romychs/Scorpion256TPlus/KiCAD/Scorpion-256-Turbo.kicad_sch

## KiCad design KiCAD/Scorpion-256-Turbo.kicad_sch (2025-11-04)

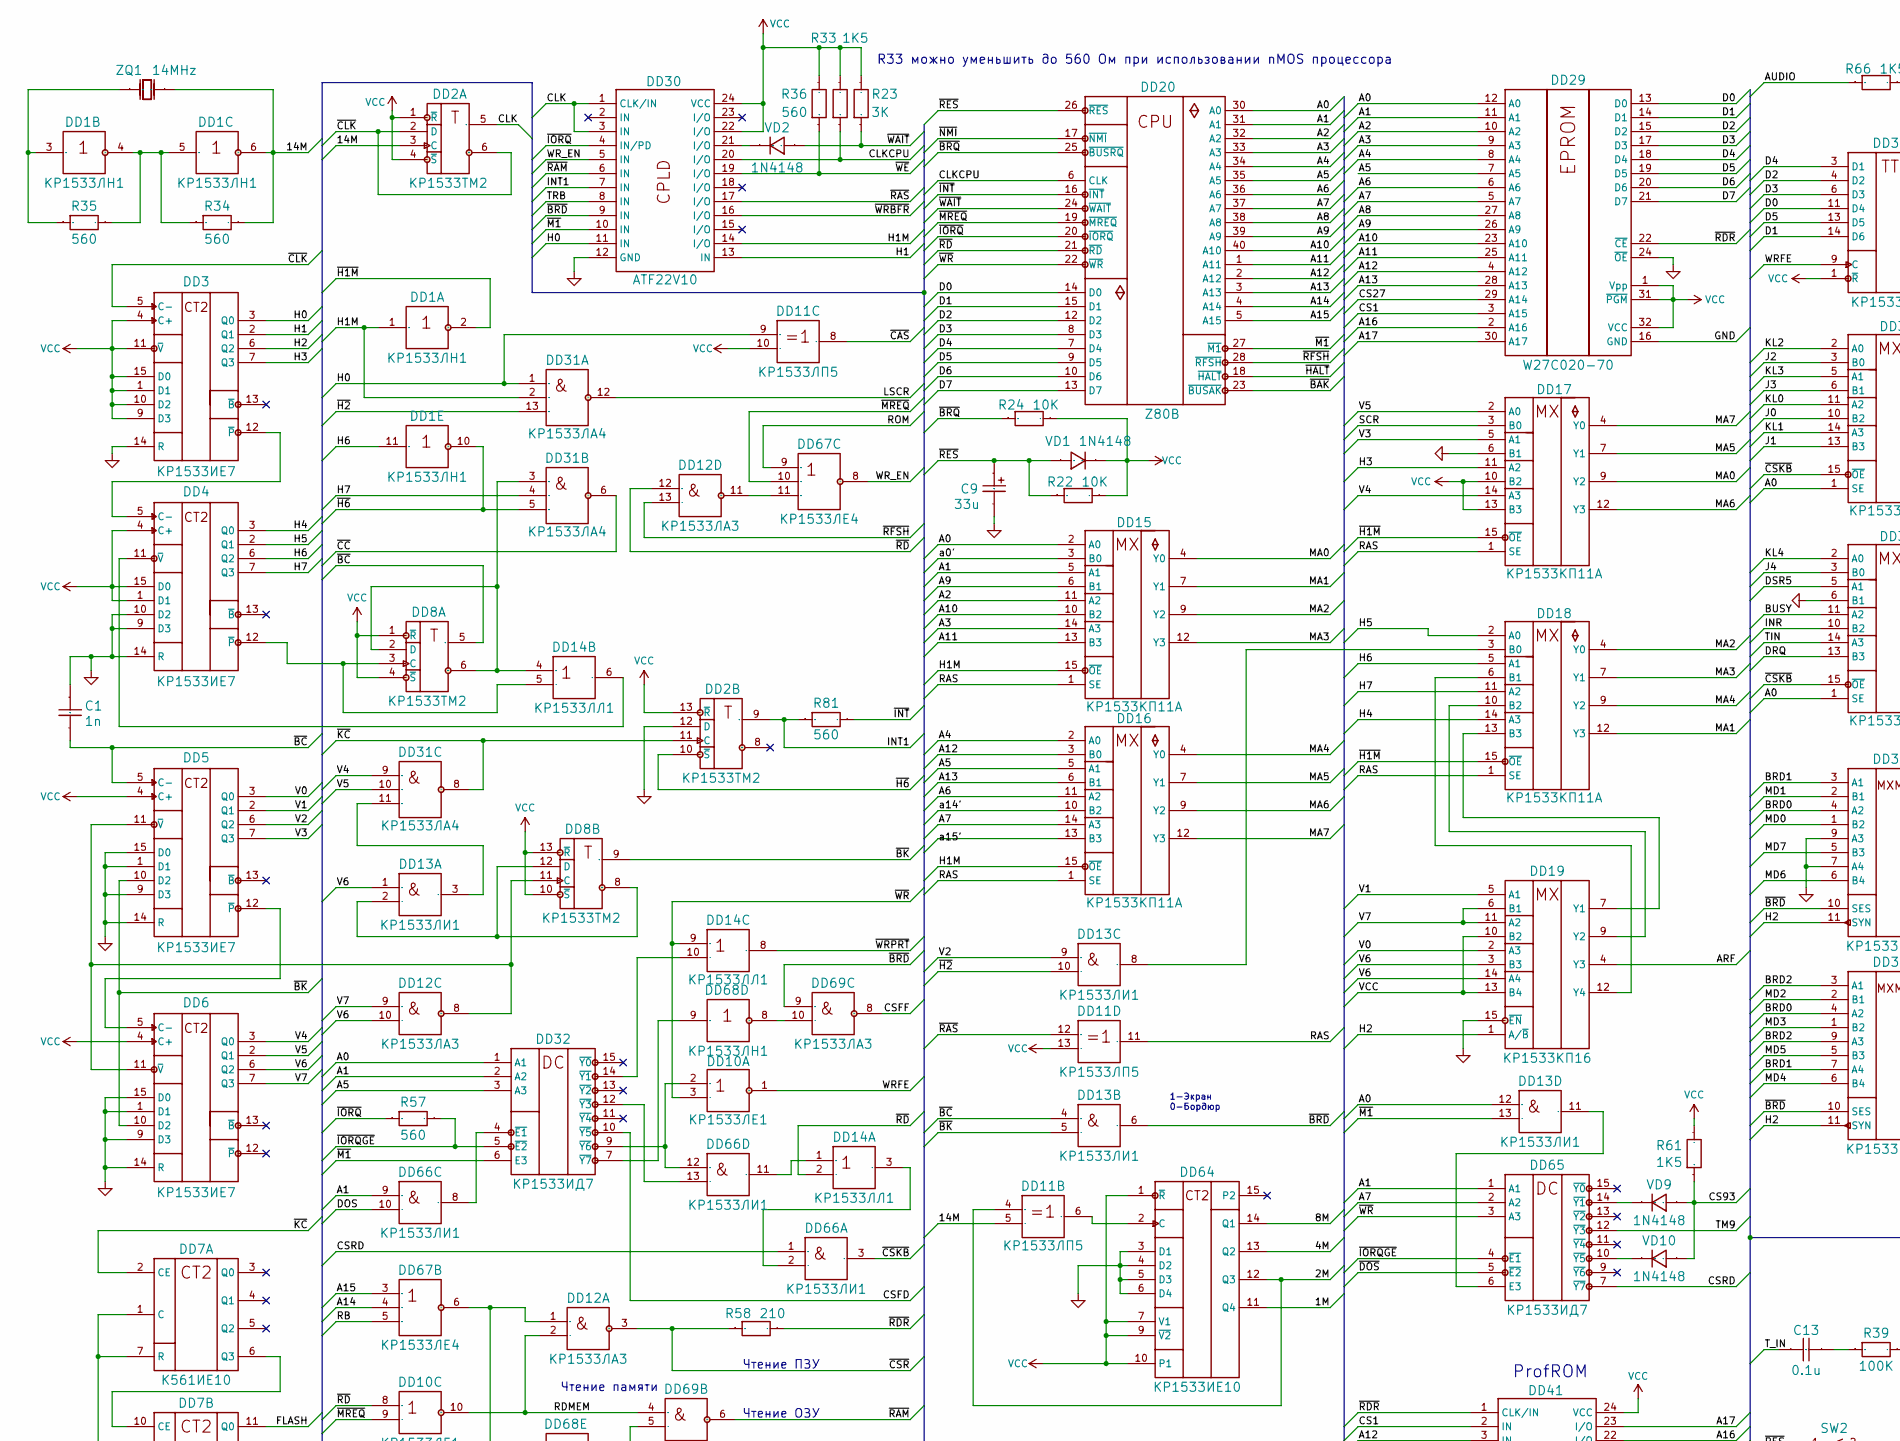
[picture p6: schematic Scorpion-256-Turbo.kicad_sch, part in row 1, column 1]

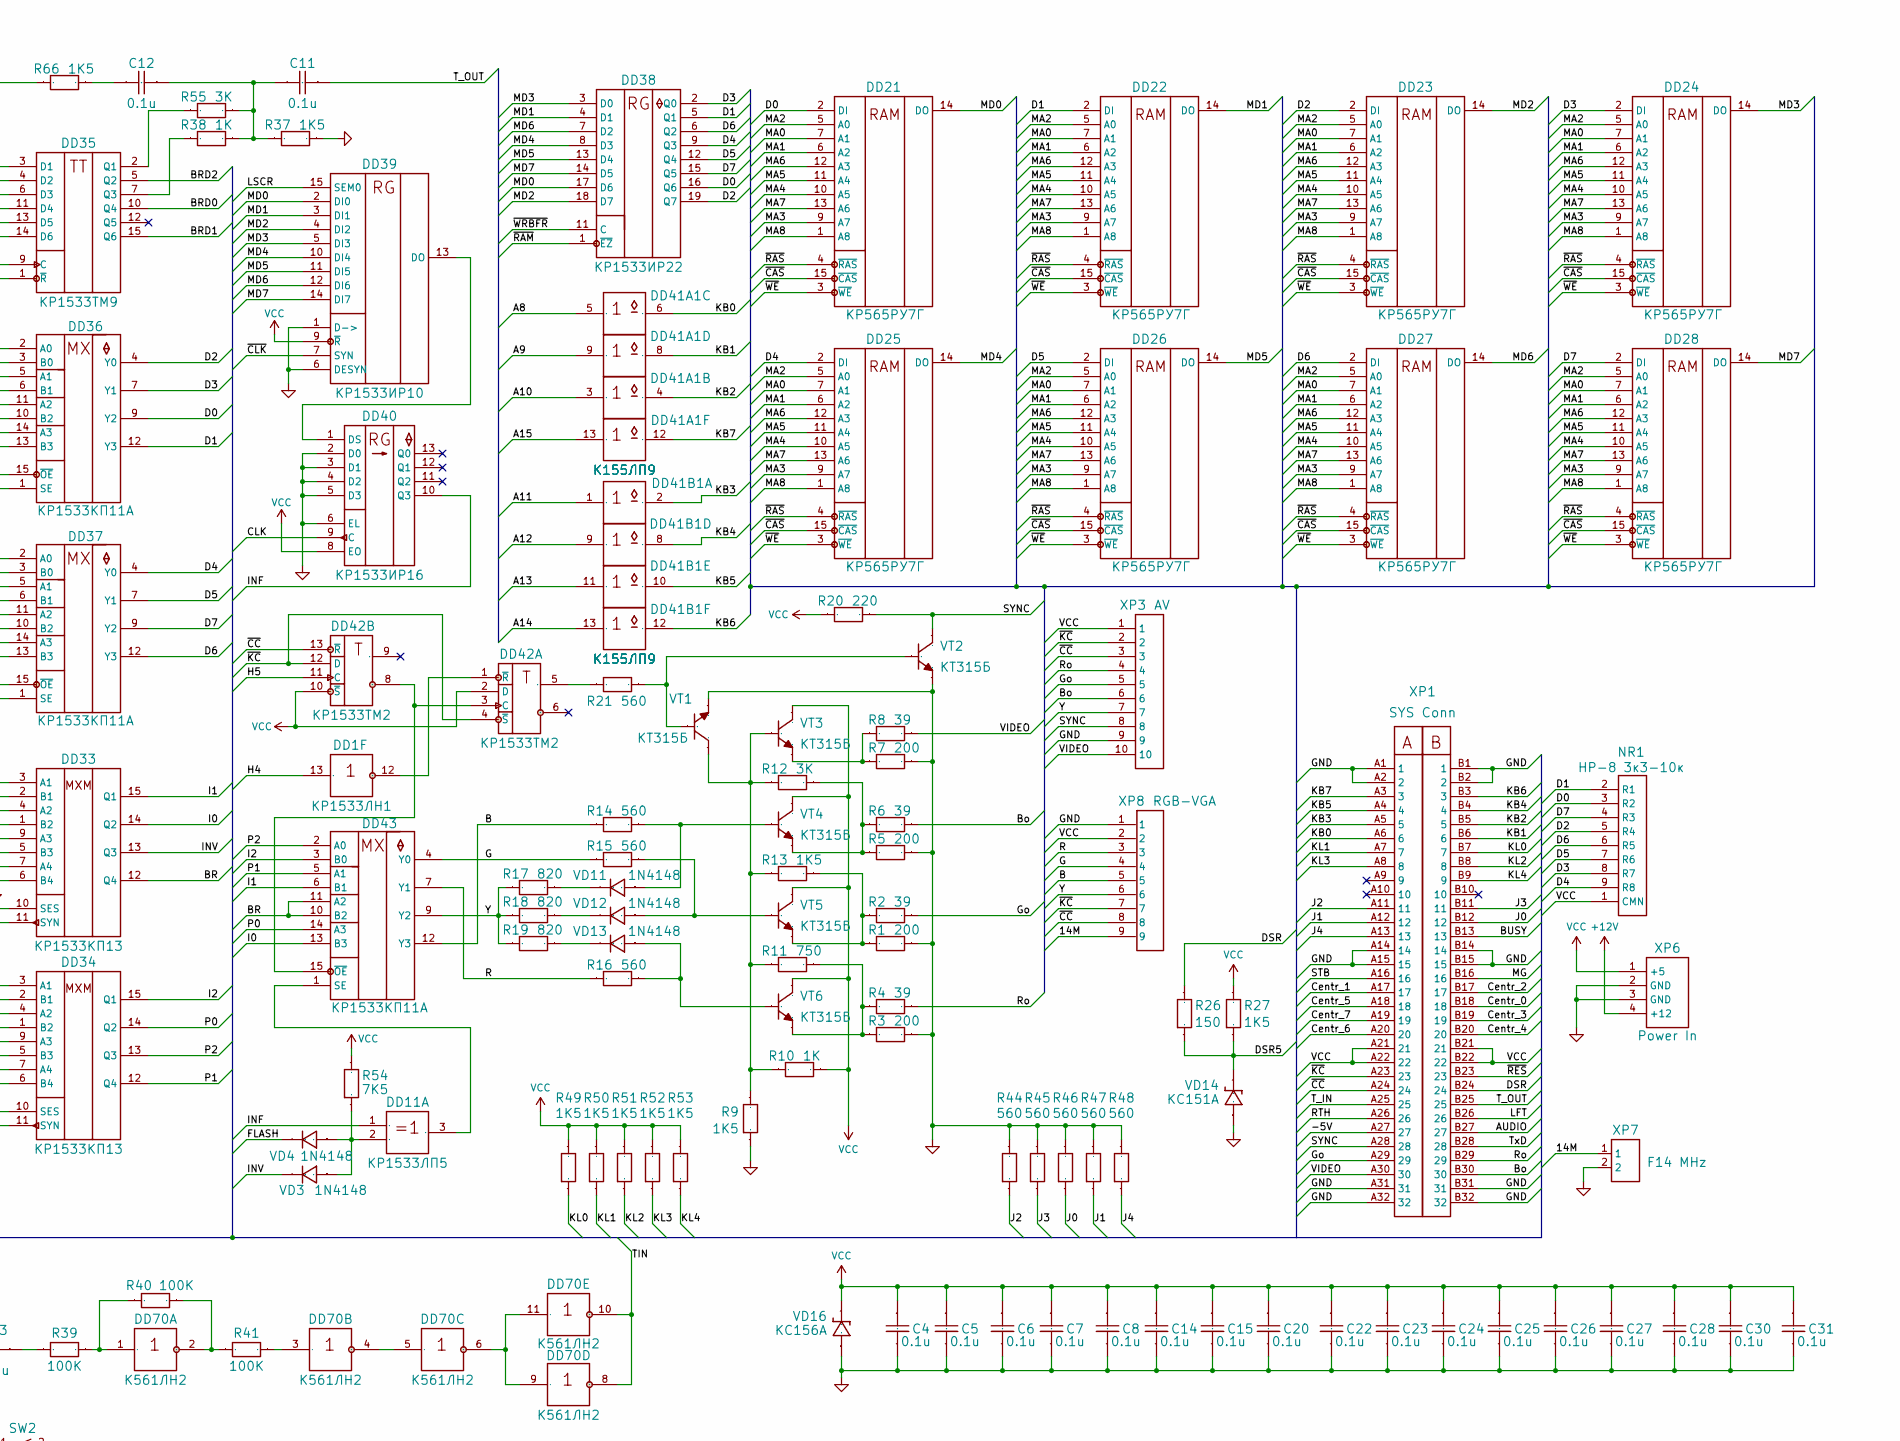
[picture p7: schematic Scorpion-256-Turbo.kicad_sch, part in row 1, column 2]

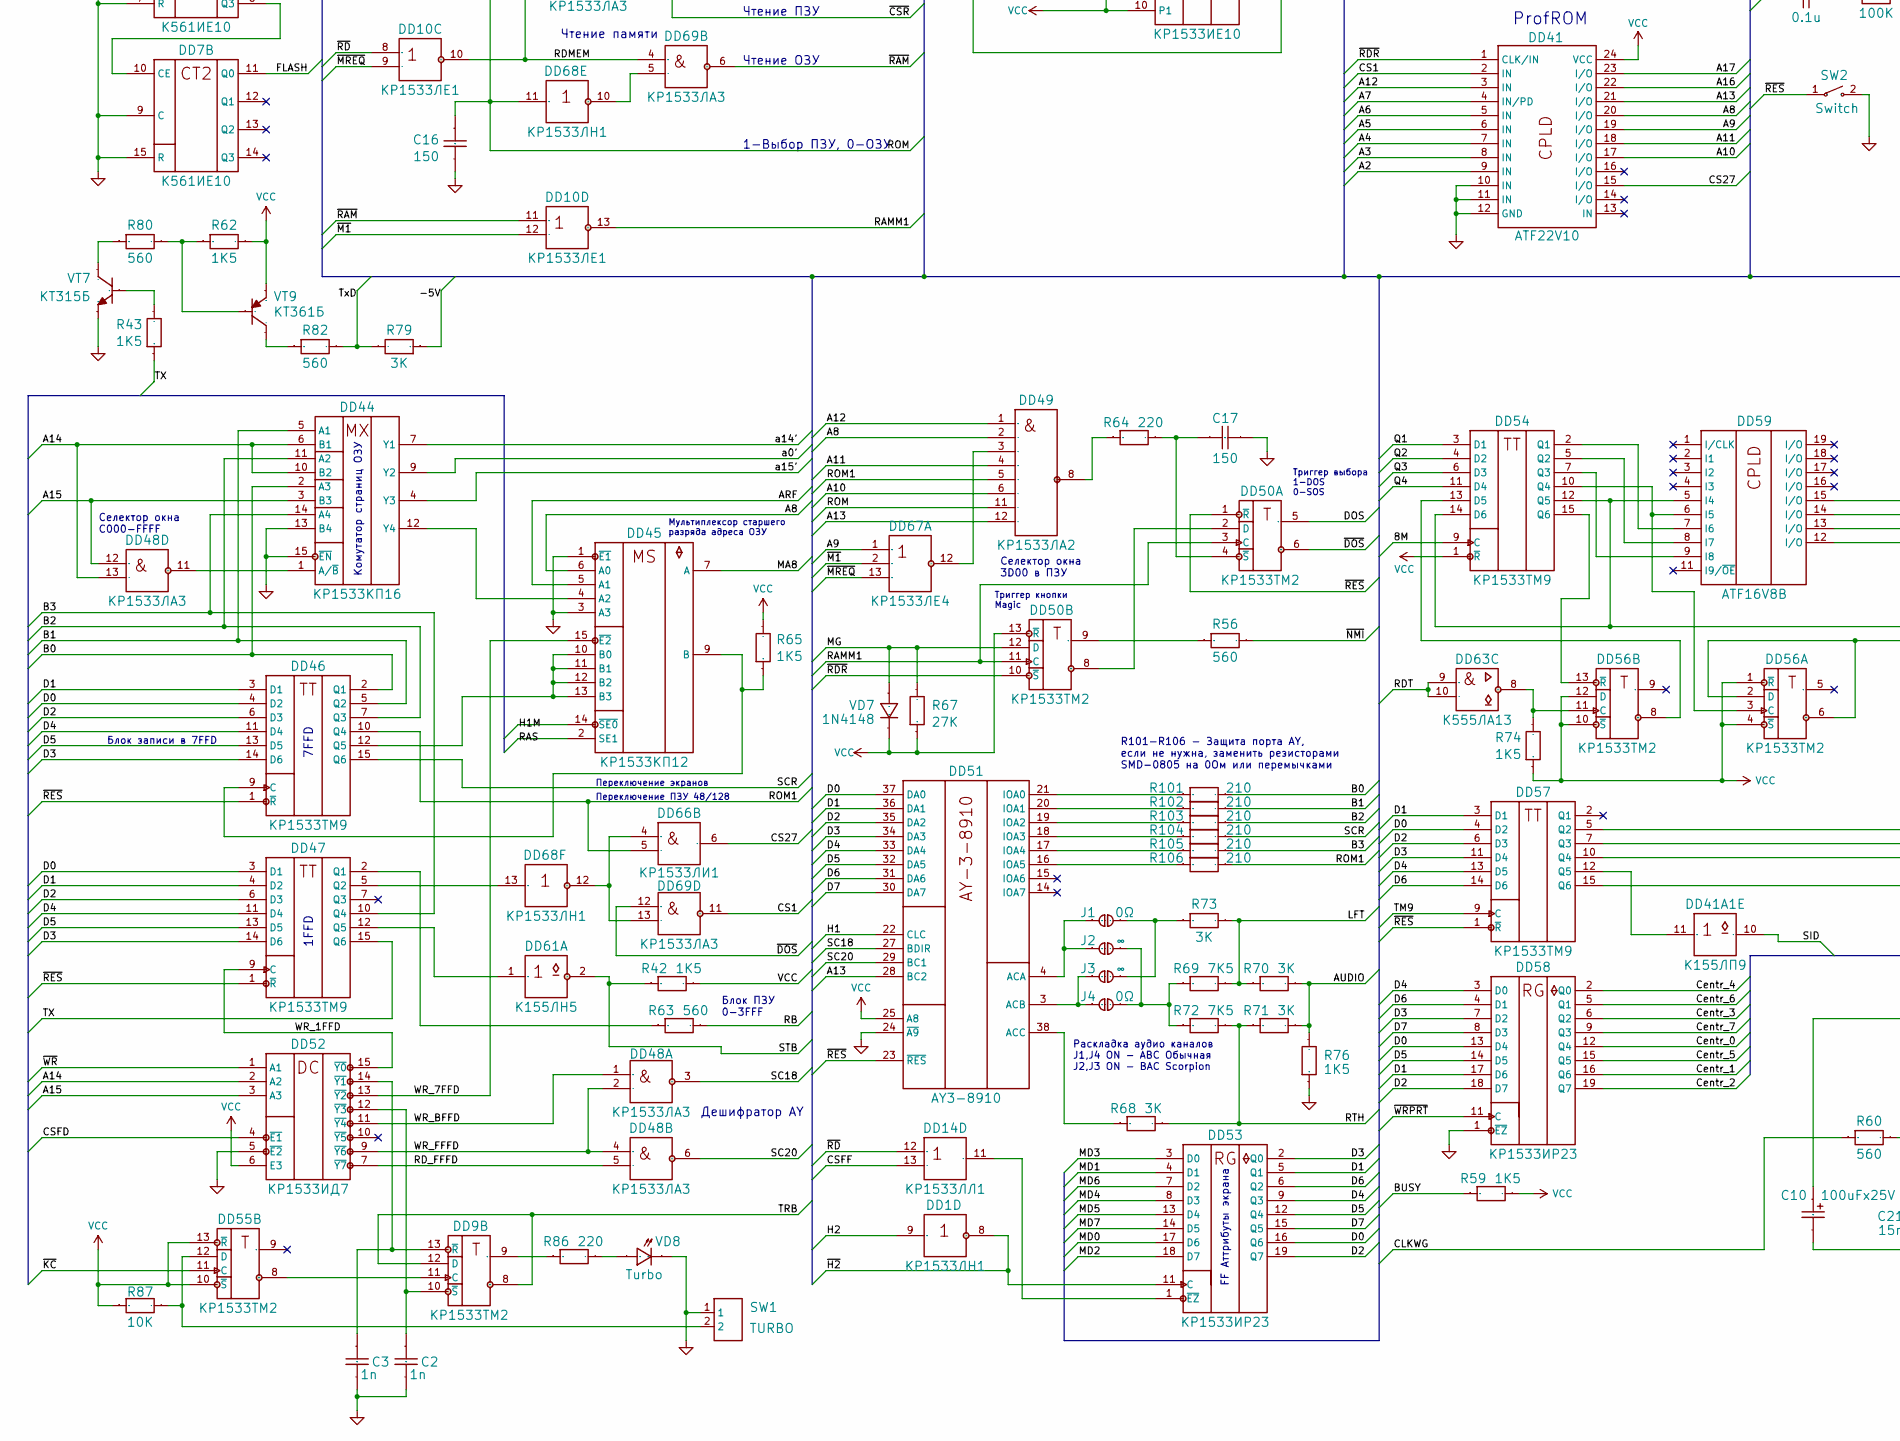
[picture p8: schematic Scorpion-256-Turbo.kicad_sch, part in row 2, column 1]

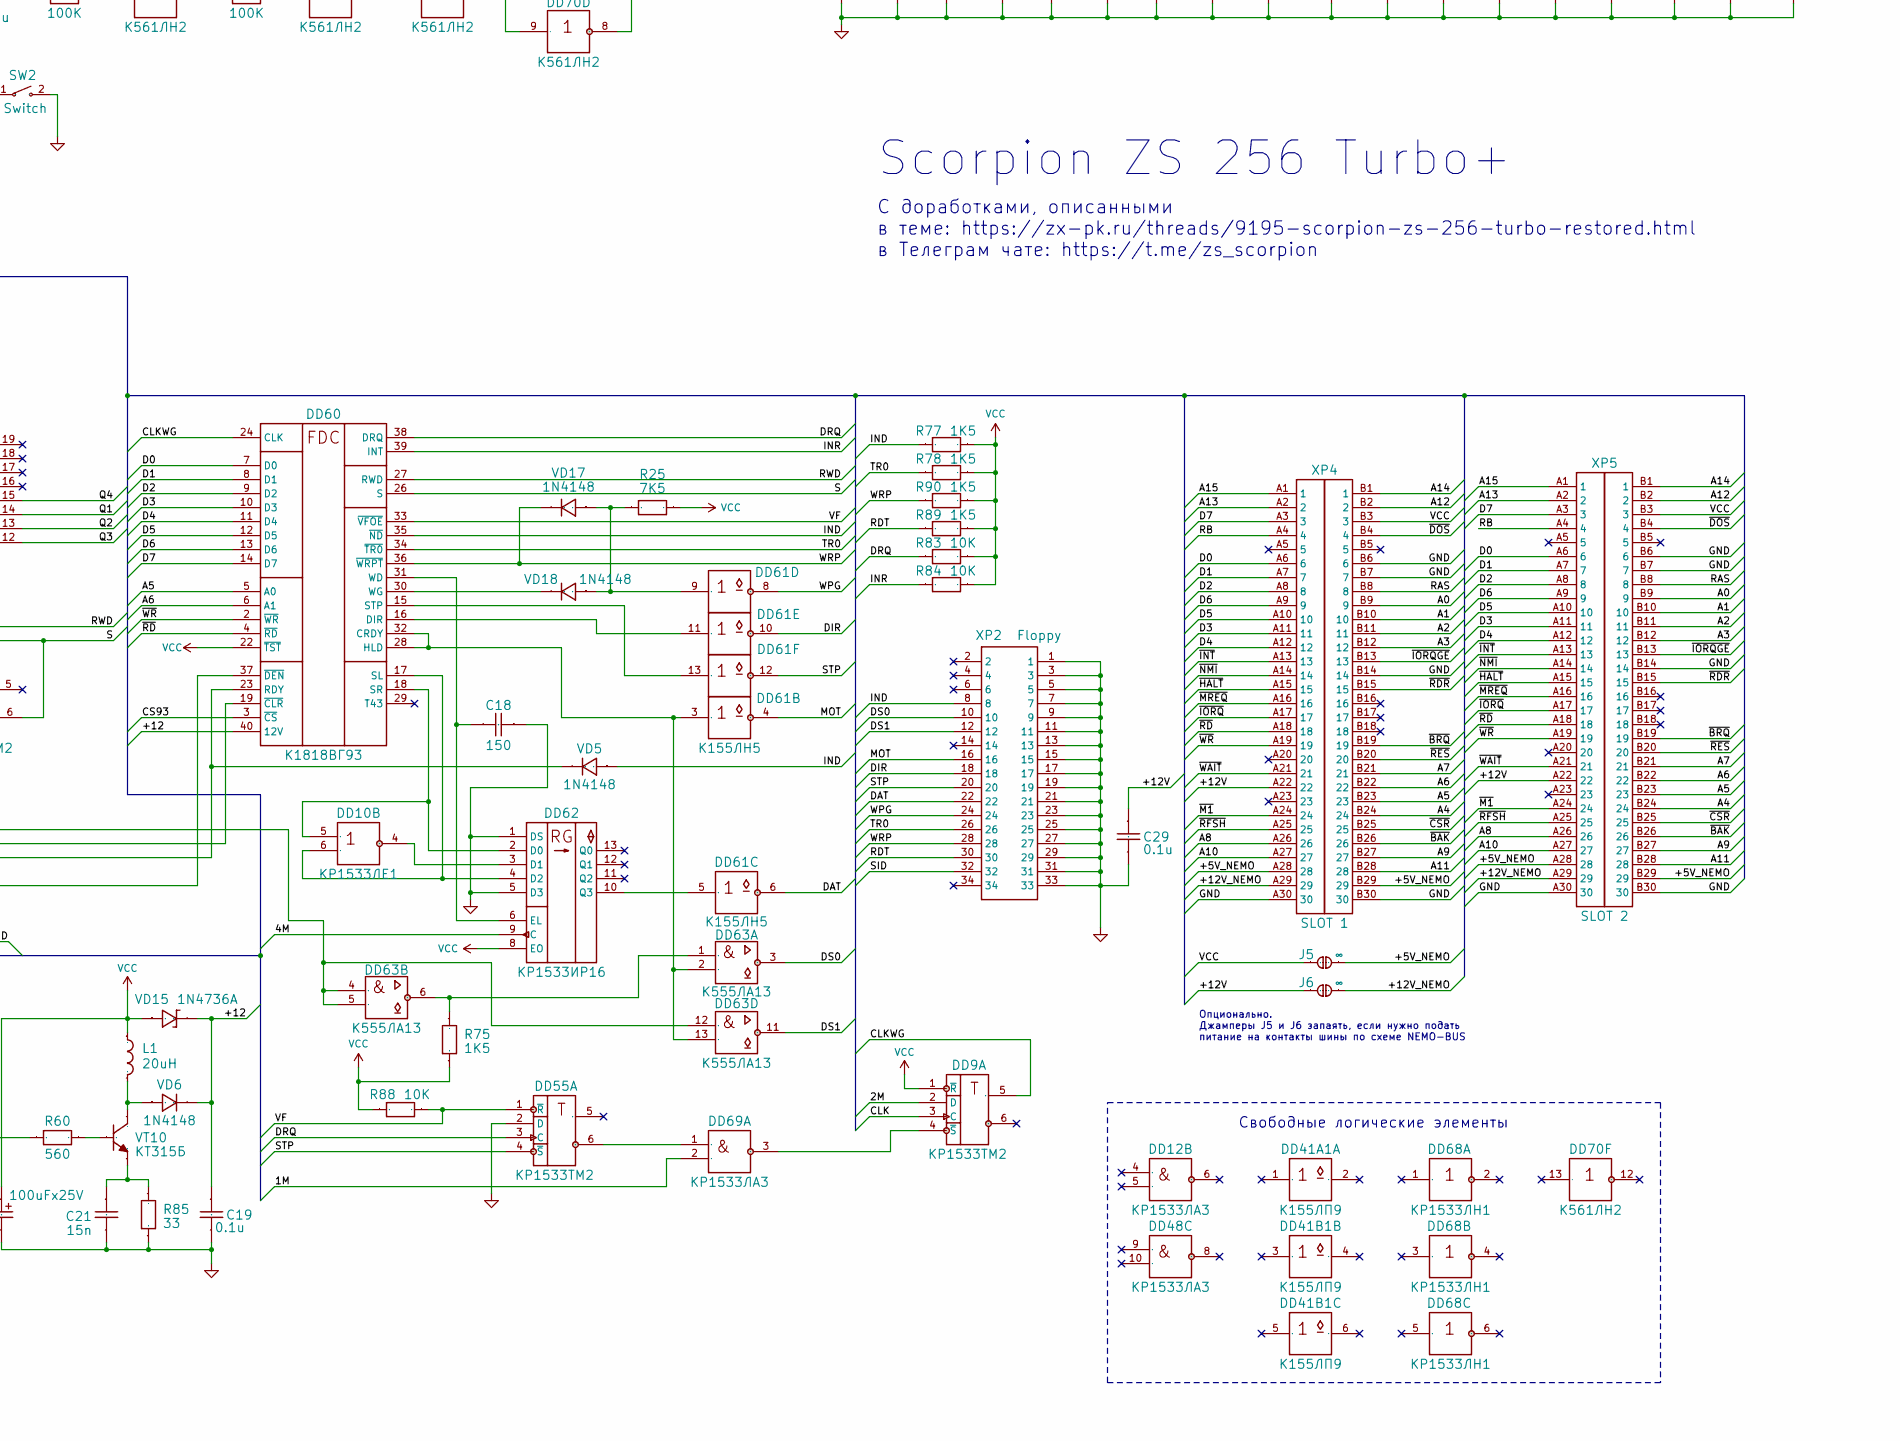
[picture p9: schematic Scorpion-256-Turbo.kicad_sch, part in row 2, column 2]

Parts:
C1, C2, C3: 1n; CAP-TH_L5.08
C4, C5, C6, C7, C8, C11, C12, C13, C14, C15, C19, C20, C22, C23, C24, C25, C26, C27, C28, C29, C30, C31: 0.1u; CAP-TH_L5.08
C9: 33u; CAP_P-TH-5x11-P2.54
C10: 100uFx25V; CAP_P-TH-5x11-P2.54
C16, C17, C18: 150; CAP-TH_L5.08
C21: 15n; CAP-TH_L5.08
DD1, DD68: КР1533ЛН1; DIP-14_W7.62mm
DD2, DD8, DD9, DD42, DD50, DD55, DD56: КР1533ТМ2; DIP-14_W7.62mm
DD3, DD4, DD5, DD6: КР1533ИЕ7; DIP-16_W7.62mm
DD7: К561ИЕ10; DIP-16_W7.62mm
DD10: КР1533ЛЕ1; DIP-14_W7.62mm
DD11: КР1533ЛП5; DIP-14_W7.62mm
DD12, DD48, DD69: КР1533ЛА3; DIP-14_W7.62mm
DD13, DD66: КР1533ЛИ1; DIP-14_W7.62mm
DD14: КР1533ЛЛ1; DIP-14_W7.62mm
DD15, DD16, DD17, DD18, DD36, DD37, DD43: КР1533КП11A; DIP-16_W7.62mm
DD19, DD44: КР1533КП16; DIP-16_W7.62mm
DD20: Z80B; DIP-40_W15.24mm_Socket
DD21, DD22, DD23, DD24, DD25, DD26, DD27, DD28: КР565РУ7Г; DIP-16_W7.62mm
DD29: W27C020-70; DIP-32_W15.24mm_Socket
DD30, DD41: ATF22V10; DIP-24_W7.62mm
DD31: КР1533ЛА4; DIP-14_W7.62mm
DD32, DD52, DD65: КР1533ИД7; DIP-16_W7.62mm
DD33, DD34: КР1533КП13; DIP-16_W7.62mm
DD35, DD46, DD47, DD54, DD57: КР1533ТМ9; DIP-16_W7.62mm
DD38: КР1533ИР22; DIP-20_STD_P7.2
DD39: КР1533ИР10; DIP-16_W7.62mm
DD40, DD62: КР1533ИР16; DIP-14_W7.62mm
DD41A1, DD41B1: К155ЛП9; DIP-14_W7.62mm
DD45: КР1533КП12; DIP-16_W7.62mm
DD49: КР1533ЛА2; DIP-14_W7.62mm
DD51: AY3-8910; DIP-40_W15.24mm_Socket
DD53, DD58: КР1533ИР23; DIP-20_STD_P7.2
DD59: ATF16V8B; DIP-20_W7.62mm
DD60: К1818ВГ93; DIP-40_W15.24mm_Socket
DD61: К155ЛН5; DIP-14_W7.62mm
DD63: К555ЛА13; DIP-14_W7.62mm
DD64: КР1533ИЕ10; DIP-16_W7.62mm
DD67: КР1533ЛЕ4; DIP-14_W7.62mm
DD70: К561ЛН2; DIP-14_W7.62mm
J1, J4: 0Ω; JUMP_0603
J2, J3, J5, J6: ∞; JUMP_0603
L1: 20uH; L-TH_L5.08
NR1: НР-8 3к3-10к; R_Array_SIP9
R1, R3, R5, R7: 200; RES_0.125W_P7.62
R2, R4, R6, R8: 39; RES_0.125W_P7.62
R9, R13, R27, R33, R37, R42, R43, R49, R50, R51, R52, R53, R59, R61, R62, R65, R66, R74, R75, R76, R77, R78, R89, R90: 1K5; RES_0.125W_P7.62
R10, R38: 1K; RES_0.125W_P7.62
R11: 750; RES_0.125W_P7.62
R12, R23, R55, R68, R70, R71, R73, R79: 3K; RES_0.125W_P7.62
R14, R15, R16, R21, R34, R35, R36, R44, R45, R46, R47, R48, R56, R57, R60, R63, R80, R81, R82: 560; RES_0.125W_P7.62
R17, R18, R19: 820; RES_0.125W_P7.62
R20, R64, R86: 220; RES_0.125W_P7.62
R22, R24, R83, R84, R87, R88: 10K; RES_0.125W_P7.62
R25, R54, R69, R72: 7K5; RES_0.125W_P7.62
R26: 150; RES_0.125W_P7.62
R39, R40, R41: 100K; RES_0.125W_P7.62
R58: 210; RES_0.125W_P7.62
R67: 27K; RES_0.125W_P7.62
R85: 33; RES_0.125W_P7.62
R101, R102, R103, R104, R105, R106: 210; R_0805_2012Metric_Pad1.20x1.40mm_HandSolder
SW1: TURBO; HDR-2P-M-P2.54
SW2: Switch; SW_Tactile_SPST_Angled_PTS645Vx39-2LFS
VD1, VD2, VD3, VD4, VD5, VD7, VD10, VD11, VD12, VD13, VD17, VD18: 1N4148; DIODE_TH_7.62; JLC_3DModel 982e0246bc4b4bfd9b52595e27e599f0
VD6: 1N4148; DIODE-TH_P10.16
VD8: Turbo; D-TH_LED_P2.54
VD9: 1N4148; DIODE-TH_P11.43
VD14: КС151А; DIODE_TH_7.62; JLC_3DModel 982e0246bc4b4bfd9b52595e27e599f0
VD15: 1N4736A; DIODE_TH_7.62; JLC_3DModel 982e0246bc4b4bfd9b52595e27e599f0
VD16: КС156А; DIODE_TH_7.62; JLC_3DModel 982e0246bc4b4bfd9b52595e27e599f0
VT1, VT2, VT3, VT4, VT5, VT6, VT7, VT10: КТ315Б; KT315_SLIM_STD; JLC_3DModel 4e458c2857b847c983e65719763eb26c
VT9: КТ361Б; KT315_SLIM_STD; JLC_3DModel 4e458c2857b847c983e65719763eb26c
XP1: SYS Conn; CONN_TH_DIN41612_32x2_ANG_INV
XP2: Floppy; IDC-Header_2x17_P2.54mm_Vertical
XP3: AV; PinSocket_1x10_P2.54mm_Vertical
XP4: SLOT 1; SL62_P2.54_R2
XP5: SLOT 2; SL62_P2.54_R2
XP6: Power In; JVC_MINI-TH-4P
XP7: F14 MHz; HDR-2P-M-P2.54
XP8: RGB-VGA; PinSocket_1x09_P2.54mm_Vertical
ZQ1: 14MHz; HC49-S

Connections:
1M: DD64.11 (Q4), DD69.2
2M: DD9.2 (D), DD11.4 (1), DD64.12 (Q3)
4M: DD62.9 (C), DD64.13 (Q2)
8M: DD54.9 (C), DD64.14 (Q1)
14M: DD1.6 (2), DD2.3 (С), DD11.5 (2), R34.2, XP7.1, XP8.9, ZQ1.1 (OSC1)
+5V_NEMO: J5.2, XP4.A28 (28), XP4.B29 (29), XP5.A28 (28), XP5.B29 (29)
+12: C19.1, DD60.40 (12V), VD6.2 (K), VD15.2 (K)
+12V: C29.1, J6.1, XP4.A22 (22), XP5.A22 (22), XP6.4 (+12)
+12V_NEMO: J6.2, XP4.A29 (29), XP5.A29 (29)
-5V: R79.1, XP1.A27 (27)
A0: DD13.12 (1), DD15.2 (A0), DD20.30 (A0), DD29.12 (A0), DD32.1 (A1), DD36.1 (SE), DD37.1 (SE), XP4.B9 (9), XP5.B9 (9)
A1: DD15.5 (A1), DD20.31 (A1), DD29.11 (A1), DD32.2 (A2), DD65.1 (A1), DD66.9 (1), XP4.B10 (10), XP5.B10 (10)
A2: DD15.11 (A2), DD20.32 (A2), DD29.10 (A2), DD41.9 (IN), XP4.B11 (11), XP5.B11 (11)
A3: DD15.14 (A3), DD20.33 (A3), DD29.9 (A3), DD41.8 (IN), XP4.B12 (12), XP5.B12 (12)
A4: DD16.2 (A0), DD20.34 (A4), DD29.8 (A4), DD41.7 (IN), XP4.B24 (24), XP5.B24 (24)
A5: DD16.5 (A1), DD20.35 (A5), DD29.7 (A5), DD32.3 (A3), DD41.6 (IN), DD60.5 (A0), XP4.B23 (23), XP5.B23 (23)
A6: DD16.11 (A2), DD20.36 (A6), DD29.6 (A6), DD41.5 (IN), DD60.6 (A1), XP4.B22 (22), XP5.B22 (22)
A7: DD16.14 (A3), DD20.37 (A7), DD29.5 (A7), DD41.4 (IN/PD), DD65.2 (A2), XP4.B21 (21), XP5.B21 (21)
A8: DD20.38 (A8), DD29.27 (A8), DD41.20 (I/O), DD41A1.5 (1), DD45.6 (A0), DD49.2, XP4.A26 (26), XP5.A26 (26)
A9: DD15.6 (B1), DD20.39 (A9), DD29.26 (A9), DD41.19 (I/O), DD41A1.9 (1), DD67.1 (I1), XP4.B27 (27), XP5.B27 (27)
A10: DD15.10 (B2), DD20.40 (A10), DD29.23 (A10), DD41.17 (I/O), DD41A1.3 (1), DD49.6, XP4.A27 (27), XP5.A27 (27)
A11: DD15.13 (B3), DD20.1 (A11), DD29.25 (A11), DD41.18 (I/O), DD41B1.1, DD49.4, XP4.B28 (28), XP5.B28 (28)
A12: DD16.3 (B0), DD20.2 (A12), DD29.4 (A12), DD41.3 (IN), DD41B1.9 (1), DD49.1, XP4.B2 (2), XP5.B2 (2)
A13: DD16.6 (B1), DD20.3 (A13), DD29.28 (A13), DD41.21 (I/O), DD41B1.11 (1), DD49.12 (8), DD51.28 (BC2), XP4.A2 (2), XP5.A2 (2)
A14: DD20.4 (A14), DD41B1.13 (1), DD44.6 (B1), DD44.10 (B2), DD48.13 (2), DD52.2 (A2), DD67.4 (I2), XP4.B1 (1), XP5.B1 (1)
A15: DD20.5 (A15), DD41A1.13 (1), DD44.3 (B3), DD48.12 (1), DD52.3 (A3), DD67.3 (I1), XP4.A1 (1), XP5.A1 (1)
A16: DD29.2 (A16), DD41.22 (I/O)
A17: DD29.30 (A17), DD41.23 (I/O)
ARF: DD19.4 (Y3), DD45.5 (A1)
AUDIO: R66.1, R70.2, R71.2, R76.2, XP1.B27 (27)
B: DD43.12 (Y3), R14.1, XP8.5
B0: DD44.2 (A3), DD46.2 (Q1), R101.2
B1: DD44.5 (A1), DD46.5 (Q2), R102.2
B2: DD44.11 (A2), DD46.7 (Q3), R103.2
B3: DD44.14 (A4), DD47.10 (Q4), R105.2
BR: DD33.12 (Q4), DD43.10 (B2), DD43.11 (A2)
BRD0: DD33.4 (A2), DD34.4 (A2), DD35.10 (Q4)
BRD1: DD33.3 (A1), DD34.7 (A4), DD35.15 (Q6)
BRD2: DD34.3 (A1), DD34.9 (A3), DD35.5 (Q2)
BUSY: DD37.11 (A2), R59.1, XP1.B13 (13)
Bo: R6.2, XP1.B30 (30), XP3.6
CLK: DD2.5 (Q), DD9.3 (С), DD30.1 (CLK/IN), DD30.3 (IN), DD40.9 (C)
CLKCPU: DD20.6 (CLK), DD30.20 (I/O), R33.1
CLKWG: DD9.5 (Q), DD60.24 (CLK), R60.1
CS1: DD29.3 (A15), DD41.2 (IN), DD69.11 (3)
CS27: DD29.29 (A14), DD41.15 (I/O), DD66.6 (3)
CS93: DD60.3 (~CS), R61.1, VD9.1 (A), VD10.1 (A)
CSFD: DD32.10 (~Y5), DD52.4 (~E1)
CSFF: DD14.13 (2), DD69.8 (3)
CSRD: DD65.7 (~Y7), DD66.1
Centr_0: DD58.12 (Q4), XP1.B18 (18)
Centr_1: DD58.16 (Q6), XP1.A17 (17)
Centr_2: DD58.19 (Q7), XP1.B17 (17)
Centr_3: DD58.6 (Q2), XP1.B19 (19)
Centr_4: DD58.2 (Q0), XP1.B20 (20)
Centr_5: DD58.15 (Q5), XP1.A18 (18)
Centr_6: DD58.5 (Q1), XP1.A20 (20)
Centr_7: DD58.9 (Q3), XP1.A19 (19)
D0: DD20.14 (D0), DD21.2 (DI), DD29.13 (D0), DD35.11 (D4), DD36.9 (Y2), DD38.16 (Q6), DD46.4 (D2), DD47.3 (D1), DD51.37 (DA0), DD53.16 (Q6), DD57.4 (D2), DD58.13 (D4), DD60.7 (D0), NR1.3 (R2), XP4.A6 (6), XP5.A6 (6)
D1: DD20.15 (D1), DD22.2 (DI), DD29.14 (D1), DD35.14 (D6), DD36.12 (Y3), DD38.5 (Q1), DD46.3 (D1), DD47.4 (D2), DD51.36 (DA1), DD53.5 (Q1), DD57.3 (D1), DD58.17 (D6), DD60.8 (D1), NR1.2 (R1), XP4.A7 (7), XP5.A7 (7)
D2: DD20.12 (D2), DD23.2 (DI), DD29.15 (D2), DD35.4 (D2), DD36.4 (Y0), DD38.19 (Q7), DD46.6 (D3), DD47.6 (D3), DD51.35 (DA2), DD53.19 (Q7), DD57.6 (D3), DD58.18 (D7), DD60.9 (D2), NR1.5 (R4), XP4.A8 (8), XP5.A8 (8)
D3: DD20.8 (D3), DD24.2 (DI), DD29.17 (D3), DD35.6 (D3), DD36.7 (Y1), DD38.2 (Q0), DD46.14 (D6), DD47.14 (D6), DD51.34 (DA3), DD53.2 (Q0), DD57.11 (D4), DD58.7 (D2), DD60.10 (D3), NR1.8 (R7), XP4.A11 (11), XP5.A11 (11)
D4: DD20.7 (D4), DD25.2 (DI), DD29.18 (D4), DD35.3 (D1), DD37.4 (Y0), DD38.9 (Q3), DD46.11 (D4), DD47.11 (D4), DD51.33 (DA4), DD53.9 (Q3), DD57.13 (D5), DD58.3 (D0), DD60.11 (D4), NR1.9 (R8), XP4.A12 (12), XP5.A12 (12)
D5: DD20.9 (D5), DD26.2 (DI), DD29.19 (D5), DD35.13 (D5), DD37.7 (Y1), DD38.12 (Q4), DD46.13 (D5), DD47.13 (D5), DD51.32 (DA5), DD53.12 (Q4), DD58.14 (D5), DD60.12 (D5), NR1.7 (R6), XP4.A10 (10), XP5.A10 (10)
D6: DD20.10 (D6), DD27.2 (DI), DD29.20 (D6), DD37.12 (Y3), DD38.6 (Q2), DD51.31 (DA6), DD53.6 (Q2), DD57.14 (D6), DD58.4 (D1), DD60.13 (D6), NR1.6 (R5), XP4.A9 (9), XP5.A9 (9)
D7: DD20.13 (D7), DD28.2 (DI), DD29.21 (D7), DD37.9 (Y2), DD38.15 (Q5), DD51.30 (DA7), DD53.15 (Q5), DD58.8 (D3), DD60.14 (D7), NR1.4 (R3), XP4.A3 (3), XP5.A3 (3)
DAT: DD61.6 (2), XP2.22
DIR: DD61.10 (2), XP2.18
DOS: DD50.5 (Q), DD66.10 (2)
DRQ: DD37.13 (B3), DD55.3 (С), DD60.38 (DRQ), R83.1
DS0: DD63.3, XP2.10
DS1: DD63.11 (3), XP2.12
DSR: R26.2, XP1.B24 (24)
DSR5: DD37.5 (A1), R26.1, R27.1, VD14.2 (K)
FLASH: DD7.11 (Q0), VD4.2 (K)
G: DD43.4 (Y0), R15.1, XP8.4
GND: C1.1, C2.2, C3.2, C4.2, C5.2, C6.2, C7.2, C8.2, C9.2, C10.2, C14.2, C15.2, C16.2, C17.1, C18.1, C19.2, C20.2, C21.2, C22.2, C23.2, C24.2, C25.2, C26.2, C27.2, C28.2, C29.2, C30.2, C31.2, DD2.12 (D), DD3.14 (R), DD4.9 (D3), DD4.10 (D2), DD4.14 (R), DD5.1 (D1), DD5.9 (D3), DD5.14 (R), DD5.15 (D0), DD6.1 (D1), DD6.9 (D3), DD6.14 (R), DD6.15 (D0), DD7.1 (C), DD7.7 (R), DD7.9 (C), DD7.15 (R), DD17.6 (B1), DD19.15 (~EN), DD29.16 (GND), DD29.24 (~OE), DD30.12 (GND), DD33.7 (A4), DD33.9 (A3), DD37.6 (B1), DD39.1 (D->), DD39.6 (DESYN), DD40.2 (D0), DD40.3 (D1), DD40.4 (D2), DD40.5 (D3), DD40.6 (EL), DD41.10 (IN), DD41.11 (IN), DD41.12 (GND), DD44.13 (B4), DD44.15 (~EN), DD45.1 (~E1), DD45.3 (A3), DD51.24 (~A9), DD52.5 (~E2), DD55.2 (D), DD58.1 (~EZ), DD62.1 (DS), DD62.5 (D3), DD64.3 (D1), DD64.4 (D2), DD64.5 (D3), DD64.6 (D4), R1.2, R3.2, R5.2, R7.2, R9.1, R37.2, R44.2, R45.2, R46.2, R47.2, R48.2, R76.1, R85.1, SW1.1, SW2.2, VD8.2 (K), VD14.1 (A), VD16.1 (A), VT1.1 (E), VT2.1 (E), VT7.1 (E), XP1.A1 (1), XP1.A2 (2), XP1.A14 (14), XP1.A15 (15), XP1.A31 (31), XP1.A32 (32), XP1.B1 (1), XP1.B2 (2), XP1.B14 (14), XP1.B15 (15), XP1.B31 (31), XP1.B32 (32), XP2.1, XP2.3, XP2.5, XP2.7, XP2.9, XP2.11, XP2.13, XP2.15, XP2.17, XP2.19, XP2.21, XP2.23, XP2.25, XP2.27, XP2.29, XP2.31, XP2.33, XP3.9, XP4.A30 (30), XP4.B6 (6), XP4.B7 (7), XP4.B14 (14), XP4.B30 (30), XP5.A30 (30), XP5.B6 (6), XP5.B7 (7), XP5.B14 (14), XP5.B30 (30), XP6.2 (GND), XP6.3 (GND), XP7.2, XP8.1
Go: R2.2, XP1.A29 (29), XP3.5
H0: DD3.3 (Q0), DD11.9 (1), DD30.11 (IN), DD31.1 (I1)
H1: DD3.2 (Q1), DD30.13 (IN), DD51.22 (CLC)
H1M: DD1.1, DD15.15 (~OE), DD16.15 (~OE), DD30.14 (I/O), DD31.2 (I2), DD45.14 (~SE0)
H2: DD1.9 (1), DD3.6 (Q2), DD19.1 (A/~B), DD33.11 (SYN), DD34.11 (SYN)
H3: DD3.7 (Q3), DD17.11 (A2)
H4: DD1.13 (1), DD4.3 (Q0), DD18.14 (A3)
H5: DD4.2 (Q1), DD18.2 (A0), DD42.11 (С)
H6: DD1.11 (1), DD4.6 (Q2), DD18.5 (A1)
H7: DD4.7 (Q3), DD18.11 (A2), DD31.4 (I2)
I0: DD33.14 (Q2), DD43.13 (B3)
I1: DD33.15 (Q1), DD43.6 (B1)
I2: DD34.15 (Q1), DD43.3 (B0)
IND: DD60.35 (~ND), R77.1, VD5.1 (A), XP2.8
INF: DD11.1, DD40.10 (Q3)
INR: DD37.10 (B2), DD60.39 (INT), R84.1
INT1: DD2.9 (Q), DD30.7 (IN), R81.1
INV: DD33.13 (Q3), VD3.2 (K)
J0: DD36.10 (B2), R46.1, XP1.B12 (12)
J1: DD36.13 (B3), R47.1, XP1.A12 (12)
J2: DD36.3 (B0), R44.1, XP1.A11 (11)
J3: DD36.6 (B1), R45.1, XP1.B11 (11)
J4: DD37.3 (B0), R48.1, XP1.A13 (13)
KB0: DD41A1.6 (2), XP1.A6 (6)
KB1: DD41A1.8 (2), XP1.B6 (6)
KB2: DD41A1.4 (2), XP1.B5 (5)
KB3: DD41B1.2, XP1.A5 (5)
KB4: DD41B1.8 (2), XP1.B4 (4)
KB5: DD41B1.10 (2), XP1.A4 (4)
KB6: DD41B1.12 (2), XP1.B3 (3)
KB7: DD41A1.12 (2), XP1.A3 (3)
KL0: DD36.11 (A2), R49.1, XP1.B7 (7)
KL1: DD36.14 (A3), R50.1, XP1.A7 (7)
KL2: DD36.2 (A0), R51.1, XP1.B8 (8)
KL3: DD36.5 (A1), R52.1, XP1.A8 (8)
KL4: DD37.2 (A0), R53.1, XP1.B9 (9)
LFT: R69.2, R70.1, R73.2, XP1.B26 (26)
LSCR: DD31.12 (O), DD39.15 (SEM0)
MA0: DD15.4 (Y0), DD17.9 (Y2), DD21.7 (A1), DD22.7 (A1), DD23.7 (A1), DD24.7 (A1), DD25.7 (A1), DD26.7 (A1), DD27.7 (A1), DD28.7 (A1)
MA1: DD15.7 (Y1), DD18.12 (Y3), DD21.6 (A2), DD22.6 (A2), DD23.6 (A2), DD24.6 (A2), DD25.6 (A2), DD26.6 (A2), DD27.6 (A2), DD28.6 (A2)
MA2: DD15.9 (Y2), DD18.4 (Y0), DD21.5 (A0), DD22.5 (A0), DD23.5 (A0), DD24.5 (A0), DD25.5 (A0), DD26.5 (A0), DD27.5 (A0), DD28.5 (A0)
MA3: DD15.12 (Y3), DD18.7 (Y1), DD21.9 (A7), DD22.9 (A7), DD23.9 (A7), DD24.9 (A7), DD25.9 (A7), DD26.9 (A7), DD27.9 (A7), DD28.9 (A7)
MA4: DD16.4 (Y0), DD18.9 (Y2), DD21.10 (A5), DD22.10 (A5), DD23.10 (A5), DD24.10 (A5), DD25.10 (A5), DD26.10 (A5), DD27.10 (A5), DD28.10 (A5)
MA5: DD16.7 (Y1), DD17.7 (Y1), DD21.11 (A4), DD22.11 (A4), DD23.11 (A4), DD24.11 (A4), DD25.11 (A4), DD26.11 (A4), DD27.11 (A4), DD28.11 (A4)
MA6: DD16.9 (Y2), DD17.12 (Y3), DD21.12 (A3), DD22.12 (A3), DD23.12 (A3), DD24.12 (A3), DD25.12 (A3), DD26.12 (A3), DD27.12 (A3), DD28.12 (A3)
MA7: DD16.12 (Y3), DD17.4 (Y0), DD21.13 (A6), DD22.13 (A6), DD23.13 (A6), DD24.13 (A6), DD25.13 (A6), DD26.13 (A6), DD27.13 (A6), DD28.13 (A6)
MA8: DD21.1 (A8), DD22.1 (A8), DD23.1 (A8), DD24.1 (A8), DD25.1 (A8), DD26.1 (A8), DD27.1 (A8), DD28.1 (A8), DD45.7 (A)
MD0: DD21.14 (DO), DD33.1 (B2), DD38.17 (D6), DD39.2 (DI0), DD53.17 (D6)
MD1: DD22.14 (DO), DD33.2 (B1), DD38.4 (D1), DD39.3 (DI1), DD53.4 (D1)
MD2: DD23.14 (DO), DD34.2 (B1), DD38.18 (D7), DD39.4 (DI2), DD53.18 (D7)
MD3: DD24.14 (DO), DD34.1 (B2), DD38.3 (D0), DD39.5 (DI3), DD53.3 (D0)
MD4: DD25.14 (DO), DD34.6 (B4), DD38.8 (D3), DD39.10 (DI4), DD53.8 (D3)
MD5: DD26.14 (DO), DD34.5 (B3), DD38.13 (D4), DD39.11 (DI5), DD53.13 (D4)
MD6: DD27.14 (DO), DD33.6 (B4), DD38.7 (D2), DD39.12 (DI6), DD53.7 (D2)
MD7: DD28.14 (DO), DD33.5 (B3), DD38.14 (D5), DD39.14 (DI7), DD53.14 (D5)
MG: DD50.12 (D), R67.2, VD7.1 (A), XP1.B16 (16)
MOT: DD61.4 (2), XP2.16
unnamed: C2.1, DD9.10 (~S), DD52.12 (~Y3)
unnamed: C3.1, DD9.13 (~R), DD52.14 (~Y1)
unnamed: C11.2, C12.1, R37.1, R38.2, R55.2
unnamed: C12.2, R66.2
unnamed: C13.1, R39.1
unnamed: C17.2, DD50.4 (~S), R64.2
unnamed: C18.2, DD60.31 (WD), DD62.6 (EL)
unnamed: C21.1, R85.2, VT10.1 (E)
unnamed: DD1.3 (1), R35.1, ZQ1.2 (OSC2)
unnamed: DD1.4 (2), DD1.5 (1), R34.1, R35.2
unnamed: DD1.12 (3), DD42.1 (~R)
unnamed: DD3.12 (~P), DD4.5 (C-)
unnamed: DD5.12 (~P), DD6.5 (C-)
unnamed: DD7.6 (Q3), DD7.10 (CE)
unnamed: DD9.9 (Q), R86.1
unnamed: DD10.2 (1), DD32.9 (~Y6), DD66.12 (1)
unnamed: DD10.4 (3), DD62.3 (D1)
unnamed: DD10.5 (1), DD60.18 (SR), DD62.2 (D0)
unnamed: DD10.6 (2), DD60.17 (SL), DD62.4 (D2)
unnamed: DD11.2, R54.1, VD3.1 (A), VD4.1 (A)
unnamed: DD11.3, DD43.1 (SE)
unnamed: DD11.6 (3), DD64.2 (C)
unnamed: DD5.11 (~V), DD6.11 (~V), DD8.11 (С), DD12.8 (3)
unnamed: DD12.11 (3), DD67.11 (I3)
unnamed: DD8.8 (~Q), DD8.12 (D), DD13.2
unnamed: DD13.3, DD31.11 (I3)
unnamed: DD13.8 (3), DD18.3 (B0)
unnamed: DD13.11 (3), DD65.6 (E3)
unnamed: DD14.1, DD66.11 (3)
unnamed: DD14.3, DD66.2
unnamed: DD8.2 (D), DD8.6 (~Q), DD14.4 (1), DD31.3 (I1)
unnamed: DD4.12 (~P), DD8.3 (С), DD14.5 (2)
unnamed: DD4.11 (~V), DD14.6 (3)
unnamed: DD14.10 (2), DD32.14 (~Y1)
unnamed: DD14.11 (3), DD53.1 (~EZ)
unnamed: DD18.6 (B1), DD19.12 (Y4)
unnamed: DD18.10 (B2), DD19.9 (Y2)
unnamed: DD18.13 (B3), DD19.7 (Y1)
unnamed: DD30.21 (I/O), VD2.2 (K)
unnamed: DD32.4 (~E1), DD66.8 (3)
unnamed: DD32.7 (~Y7), DD68.9 (1)
unnamed: DD32.12 (~Y3), DD66.13 (2)
unnamed: DD35.2 (Q1), R55.1
unnamed: DD35.7 (Q3), R38.1
unnamed: DD39.13 (DO), DD40.1 (DS)
unnamed: DD41A1.11 (1), DD57.12 (Q5)
unnamed: DD42.3 (С), DD42.8 (~Q), DD43.15 (~OE)
unnamed: DD42.5 (Q), R21.1
unnamed: DD44.1 (A/~B), DD48.11 (3)
unnamed: DD44.12 (Y4), DD45.4 (A2)
unnamed: DD45.9 (B), DD46.9 (C), R65.1
unnamed: DD45.10 (B0), DD45.11 (B1), DD45.12 (B2), DD45.13 (B3), DD46.12 (Q5)
unnamed: DD47.2 (Q1), R63.1
unnamed: DD47.5 (Q2), DD68.13 (1)
unnamed: DD47.12 (Q5), DD61.1
unnamed: DD49.3, DD67.12 (O)
unnamed: DD49.8, R64.1
unnamed: DD50.2 (D), DD50.8 (~Q)
unnamed: DD50.9 (Q), R56.1
unnamed: DD51.3 (ACB), J3.1, J4.1
unnamed: DD51.4 (ACA), J1.1, J2.1
unnamed: DD51.16 (IOA5), R106.1
unnamed: DD51.17 (IOA4), R105.1
unnamed: DD51.18 (IOA3), R104.1
unnamed: DD51.19 (IOA2), R103.1
unnamed: DD51.20 (IOA1), R102.1
unnamed: DD51.21 (IOA0), R101.1
unnamed: DD51.38 (ACC), R68.1
unnamed: DD54.2 (Q1), DD59.7 (I6)
unnamed: DD54.5 (Q2), DD59.8 (I7)
unnamed: DD54.7 (Q3), DD59.9 (I8)
unnamed: DD54.10 (Q4), DD56.3 (С), DD59.6 (I5)
unnamed: DD54.13 (D5), DD56.8 (~Q)
unnamed: DD54.15 (Q6), DD56.13 (~R)
unnamed: DD55.6 (~Q), DD69.1
unnamed: DD9.11 (С), DD55.8 (~Q)
unnamed: DD55.12 (D), R87.2, SW1.2
unnamed: DD56.11 (С), DD63.8 (3), R74.2
unnamed: DD57.5 (Q2), DD63.4 (1), DD63.5 (2), DD63.12 (1)
unnamed: DD57.7 (Q3), DD60.19 (~CLR)
unnamed: DD57.10 (Q4), DD60.23 (RDY), VD5.2 (K)
unnamed: DD57.15 (Q6), DD60.37 (~DEN)
unnamed: DD60.15 (STP), DD61.13 (1)
unnamed: DD60.16 (DIR), DD61.11 (1)
unnamed: DD60.28 (HLD), DD60.32 (CRDY), DD61.3 (1), DD63.2, DD63.13 (2)
unnamed: DD60.30 (WG), VD18.2 (K)
unnamed: DD61.5 (1), DD62.10 (Q3)
unnamed: DD61.9 (1), R25.1, VD17.1 (A), VD18.1 (A)
unnamed: DD63.1, DD63.6 (3), R75.2
unnamed: DD65.10 (~Y5), VD10.2 (K)
unnamed: DD65.14 (~Y1), VD9.2 (K)
unnamed: DD66.4 (1), DD68.12 (3), DD69.13 (2)
unnamed: DD68.8 (2), DD69.10 (2)
unnamed: DD68.10 (2), DD69.5 (2)
unnamed: DD9.4 (~S), DD69.3
unnamed: DD70.1 (I), R39.2, R40.1
unnamed: DD70.2 (O), R40.2, R41.1
unnamed: DD70.3 (I), R41.2
unnamed: DD70.4 (O), DD70.5 (I)
unnamed: DD70.6 (O), DD70.9 (I), DD70.11 (I)
unnamed: J1.2, J3.2, R73.1
unnamed: J2.2, J4.2, R69.1, R72.1
unnamed: L1.2, VD6.1 (A), VT10.2 (C)
unnamed: R1.1, R2.1, R13.2, VT5.1 (E)
unnamed: R7.1, R8.1, VT3.1 (E)
unnamed: R9.2, R10.1, R11.1, R12.1, R13.1, VT1.2 (C), VT3.3 (B)
unnamed: R3.1, R4.1, R11.2, VT6.1 (E)
unnamed: R5.1, R6.1, R12.2, VT4.1 (E)
unnamed: R14.2, VD11.1 (A), VT4.3 (B)
unnamed: R15.2, VD12.1 (A), VT5.3 (B)
unnamed: R16.2, VD13.1 (A), VT6.3 (B)
unnamed: R17.2, VD11.2 (K)
unnamed: R18.2, VD12.2 (K)
unnamed: R19.2, VD13.2 (K)
unnamed: R21.2, VT1.3 (B), VT2.3 (B)
unnamed: R43.2, VT7.3 (B)
unnamed: R60.2, VT10.3 (B)
unnamed: R62.1, R80.2, VT9.3 (B)
unnamed: R80.1, VT7.2 (C)
unnamed: R82.1, VT9.2 (C)
unnamed: R86.2, VD8.1 (A)
P0: DD34.14 (Q2), DD43.14 (A3)
P1: DD34.12 (Q4), DD43.5 (A1)
P2: DD34.13 (Q3), DD43.2 (A0)
Q1: DD54.3 (D1), DD59.14 (I/O)
Q2: DD54.4 (D2), DD59.13 (I/O)
Q3: DD54.6 (D3), DD59.12 (I/O)
Q4: DD54.11 (D4), DD59.15 (I/O)
R: DD43.7 (Y1), R16.1, XP8.3
RAMM1: DD10.13 (3), DD50.3 (С), DD50.11 (С)
RAS: DD11.11 (3), DD15.1 (SE), DD16.1 (SE), DD17.1 (SE), DD18.1 (SE), DD45.2 (SE1), XP4.B8 (8), XP5.B8 (8)
RB: DD67.5 (I3), R63.2, XP4.A4 (4), XP5.A4 (4)
RDMEM: DD10.10 (3), DD12.2, DD69.4 (1)
RDT: DD63.9 (1), DD63.10 (2), R89.1, XP2.30
RD_FFFD: DD48.5 (2), DD52.7 (~Y7)
ROM: C16.1, DD12.1, DD49.11 (7), DD67.6 (O), DD67.9 (I1), DD68.11 (1)
ROM1: DD46.10 (Q4), DD49.5, DD66.5 (2), R106.2
RTH: R68.2, R71.1, R72.2, XP1.A26 (26)
RWD: DD54.12 (Q5), DD54.14 (D6), DD59.5 (I4), DD60.27 (RWD)
Ro: R4.2, XP1.B29 (29), XP3.4
S: DD56.2 (D), DD56.6 (~Q), DD60.26 (S)
SC18: DD48.3, DD51.27 (BDIR)
SC20: DD48.6 (3), DD51.29 (BC1)
SCR: DD17.3 (B0), DD46.15 (Q6), R104.2
SID: DD41A1.10 (2), XP2.32
STB: DD61.2, R42.1, XP1.A16 (16)
STP: DD55.4 (~S), DD61.12 (2), XP2.20
SYNC: R20.2, VT2.2 (C), XP1.A28 (28), XP3.8
TIN: DD37.14 (A3), DD70.8 (O), DD70.10 (O)
TM9: DD57.9 (C), DD65.12 (~Y3)
TR0: DD60.34 (~TR0), R78.1, XP2.26
TRB: DD9.8 (~Q), DD9.12 (D), DD30.8 (IN)
TX: DD47.15 (Q6), R43.1
T_IN: C13.2, XP1.A25 (25)
T_OUT: C11.1, XP1.B25 (25)
TxD: R79.2, R82.2, XP1.B28 (28)
V0: DD5.3 (Q0), DD19.2 (A3)
V1: DD5.2 (Q1), DD19.5 (A1)
V2: DD5.6 (Q2), DD13.9 (1)
V3: DD5.7 (Q3), DD17.5 (A1)
V4: DD6.3 (Q0), DD17.14 (A3), DD31.9 (I1)
V5: DD6.2 (Q1), DD17.2 (A0), DD31.10 (I2)
V6: DD6.6 (Q2), DD12.10 (2), DD13.1, DD19.3 (B3), DD19.14 (A4)
V7: DD6.7 (Q3), DD12.9 (1), DD19.6 (B1), DD19.11 (A2)
VCC: C4.1, C5.1, C6.1, C7.1, C8.1, C10.1, C14.1, C15.1, C20.1, C22.1, C23.1, C24.1, C25.1, C26.1, C27.1, C28.1, C30.1, C31.1, DD2.1 (~R), DD2.4 (~S), DD2.13 (~R), DD3.1 (D1), DD3.4 (C+), DD3.9 (D3), DD3.10 (D2), DD3.11 (~V), DD3.15 (D0), DD4.1 (D1), DD4.4 (C+), DD4.15 (D0), DD5.4 (C+), DD6.4 (C+), DD8.1 (~R), DD8.4 (~S), DD8.10 (~S), DD8.13 (~R), DD9.1 (~R), DD11.10 (2), DD11.13 (2), DD17.10 (B2), DD17.13 (B3), DD19.10 (B2), DD19.13 (B4), DD29.1 (Vpp), DD29.31 (~PGM), DD29.32 (VCC), DD30.22 (I/O), DD30.24 (VCC), DD35.1 (~R), DD39.9 (~R), DD40.8 (EO), DD41.24 (VCC), DD42.2 (D), DD42.10 (~S), DD50.13 (~R), DD51.25 (A8), DD52.6 (E3), DD54.1 (~R), DD55.10 (~S), DD55.13 (~R), DD56.1 (~R), DD56.4 (~S), DD56.10 (~S), DD56.12 (D), DD60.22 (~TST), DD62.8 (EO), DD64.1 (~R), DD64.7 (V1), DD64.9 (~V2), DD64.10 (P1), J5.1, L1.1, NR1.1 (CMN), R10.2, R20.1, R22.2, R23.2, R24.2, R25.2, R27.2, R33.2, R36.2, R42.2, R49.2, R50.2, R51.2, R52.2, R53.2, R54.2, R59.2, R61.2, R62.2, R65.2, R67.1, R74.1, R75.1, R77.2, R78.2, R83.2, R84.2, R87.1, R88.1, R89.2, R90.2, VD1.2 (K), VD7.2 (K), VD15.1 (A), VD16.2 (K), VT3.2 (C), VT4.2 (C), VT5.2 (C), VT6.2 (C), VT9.1 (E), XP1.A21 (21), XP1.A22 (22), XP1.B21 (21), XP1.B22 (22), XP3.1, XP4.B3 (3), XP5.B3 (3), XP6.1 (+5), XP8.2
VF: DD55.1 (~R), DD60.33 (~VFOE), R88.2
VIDEO: R8.2, XP1.A30 (30), XP3.10
WPG: DD61.8 (2), XP2.24
WRFE: DD10.1 (3), DD35.9 (C)
WRP: DD60.36 (~WRPT), R90.1, VD17.2 (K), XP2.28
WR_1FFD: DD47.9 (C), DD52.15 (~Y0)
WR_7FFD: DD45.15 (~E2), DD52.13 (~Y2)
WR_BFFD: DD48.1, DD52.11 (~Y4)
WR_EN: DD30.5 (IN), DD67.8 (O)
WR_FFFD: DD48.2, DD48.4 (1), DD52.9 (~Y6)
Y: DD43.9 (Y2), R17.1, R18.1, R19.1, XP3.7, XP8.6
a0': DD15.3 (B0), DD44.9 (Y2)
a14': DD16.10 (B2), DD44.7 (Y1)
a15': DD16.13 (B3), DD44.4 (Y3)
~BAK: DD20.23 (~BUSAK), XP4.B26 (26), XP5.B26 (26)
~BC: C1.2, DD5.5 (C-), DD8.5 (Q), DD13.4 (1)
~BK: DD5.10 (D2), DD6.10 (D2), DD8.9 (Q), DD13.5 (2)
~BRD: DD13.6 (3), DD30.9 (IN), DD33.10 (SES), DD34.10 (SES), DD69.9 (1)
~BRQ: DD20.25 (~BUSRQ), R24.1, XP4.B19 (19), XP5.B19 (19)
~CAS: DD11.8 (3), DD21.15 (~CAS), DD22.15 (~CAS), DD23.15 (~CAS), DD24.15 (~CAS), DD25.15 (~CAS), DD26.15 (~CAS), DD27.15 (~CAS), DD28.15 (~CAS)
~CC: DD31.6 (O), DD42.13 (~R), XP1.A24 (24), XP3.3, XP8.8
~CLK: DD2.2 (D), DD2.6 (~Q), DD3.5 (C-), DD39.7 (SYN)
~CSKB: DD36.15 (~OE), DD37.15 (~OE), DD66.3
~CSR: DD12.3, R58.1, XP4.B25 (25), XP5.B25 (25)
~DOS: DD50.6 (~Q), DD65.5 (~E2), DD69.12 (1), XP4.B4 (4), XP5.B4 (4)
~H1M: DD1.2, DD17.15 (~OE), DD18.15 (~OE)
~H2: DD1.8 (2), DD13.10 (2), DD31.13 (I3), DD53.11 (C)
~H6: DD1.10 (2), DD2.10 (~S), DD31.5 (I3)
~HALT: DD20.18 (~HALT), XP4.A15 (15), XP5.A15 (15)
~INT: DD20.16 (~INT), R81.2, XP4.A13 (13), XP5.A13 (13)
~IORQGE: DD32.5 (~E2), DD65.4 (~E1), R57.2, XP4.B13 (13), XP5.B13 (13)
~IORQ: DD20.20 (~IORQ), DD30.4 (IN/PD), R57.1, XP4.A17 (17), XP5.A17 (17)
~KC: DD2.11 (С), DD7.2 (CE), DD31.8 (O), DD42.4 (~S), DD42.12 (D), DD55.11 (С), XP1.A23 (23), XP3.2, XP8.7
~M1: DD10.12 (2), DD13.13 (2), DD20.27 (~M1), DD30.10 (IN), DD32.6 (E3), DD67.2 (I2), XP4.A24 (24), XP5.A24 (24)
~MREQ: DD10.9 (2), DD20.19 (~MREQ), DD67.10 (I2), DD67.13 (I3), XP4.A16 (16), XP5.A16 (16)
~NMI: DD20.17 (~NMI), R56.2, XP4.A14 (14), XP5.A14 (14)
~RAM: DD10.11 (1), DD30.6 (IN), DD38.1 (~EZ), DD69.6 (3)
~RAS: DD11.12 (1), DD21.4 (~RAS), DD22.4 (~RAS), DD23.4 (~RAS), DD24.4 (~RAS), DD25.4 (~RAS), DD26.4 (~RAS), DD27.4 (~RAS), DD28.4 (~RAS), DD30.17 (I/O)
~RDR: DD29.22 (~CE), DD41.1 (CLK/IN), DD50.10 (~S), R58.2, XP4.B15 (15), XP5.B15 (15)
~RD: DD10.8 (1), DD12.12 (1), DD14.2, DD14.12 (1), DD20.21 (~RD), DD60.4 (~RD), XP4.A18 (18), XP5.A18 (18)
~RES: C9.1, DD20.26 (~RES), DD46.1 (~R), DD47.1 (~R), DD50.1 (~R), DD51.23 (~RES), DD57.1 (~R), R22.1, SW2.1, VD1.1 (A), XP1.B23 (23), XP4.B20 (20), XP5.B20 (20)
~RFSH: DD12.13 (2), DD20.28 (~RFSH), XP4.A25 (25), XP5.A25 (25)
~WAIT: DD20.24 (~WAIT), R23.1, VD2.1 (A), XP4.A21 (21), XP5.A21 (21)
~WE: DD21.3 (~WE), DD22.3 (~WE), DD23.3 (~WE), DD24.3 (~WE), DD25.3 (~WE), DD26.3 (~WE), DD27.3 (~WE), DD28.3 (~WE), DD30.19 (I/O), R36.1
~WRBFR: DD30.16 (I/O), DD38.11 (C)
~WRPRT: DD14.8 (3), DD58.11 (C)
~WR: DD10.3 (2), DD14.9 (1), DD20.22 (~WR), DD52.1 (A1), DD60.2 (~WR), DD65.3 (A3), XP4.A19 (19), XP5.A19 (19)

Notes on the sheet:
Чтение ПЗУ
Селектор окна C000-FFFF
1FFD
Свободные логические элементы
Триггер выбора 1-DOS 0-SOS
Селектор окна 3D00 в ПЗУ
R33 можно уменьшить до 560 Ом при использовании nMOS процессора
Комутатор страниц ОЗУ
7FFD
Блок записи в 7FFD
1-Экран 0-Бордюр
Чтение памяти
ProfROM
Раскладка аудио каналов J1,J4 ON - ABC Обычная J2,J3 ON - BAC Scorpion
Чтение ОЗУ
FF Аттрибуты экрана
1-Выбор ПЗУ, 0-ОЗУ
Блок ПЗУ 0-3FFF
Scorpion ZS 256 Turbo+
Переключение экранов
Переключение ПЗУ 48/128
Дешифратор AY
R101-R106 - Защита порта AY, если не нужна, заменить резисторами SMD-0805 на 0Ом или перемычками
Триггер кнопки Magic
Мультиплексор старшего разряда адреса ОЗУ
С доработками, описанными в теме: https://zx-pk.ru/threads/9195-scorpion-zs-256-turbo-restored.html в Телеграм чате: https://t.me/zs_scorpion
Опционально. Джамперы J5 и J6 запаять, если нужно подать питание на контакты шины по схеме NEMO-BUS
